nodep/nrfburn/host/hiddev.cpp

/* Name: hiddata.c
 * Author: Christian Starkjohann
 * Creation Date: 2008-04-11
 * Tabsize: 4
 * Copyright: (c) 2008 by OBJECTIVE DEVELOPMENT Software GmbH
 * License: GNU GPL v2 (see License.txt), GNU GPL v3 or proprietary (CommercialLicense.txt)
 */

#include <stdio.h>
#include <stdint.h>
#include <string>

#include "hiddev.h"

#define USBOPEN_SUCCESS         0   	// no error
#define USBOPEN_ERR_ACCESS      1   	// not enough permissions to open device
#define USBOPEN_ERR_IO          2   	// I/O error
#define USBOPEN_ERR_NOTFOUND    3   	// device not found

#ifdef DEBUG
#define DEBUG_PRINT(arg)    printf arg
#else
#define DEBUG_PRINT(arg)
#endif

#define LOG_HID_TRAFFIC

#include "utils.h"

/* ######################################################################## */
#ifdef WIN32 /* ******##################################################### */
/* ######################################################################## */

#include <windows.h>
#include <setupapi.h>

#include "hidsdi_loc.h"
#include <ddk/hidpi.h>

/* ------------------------------------------------------------------------ */

static void convertUniToAscii(char* buffer)
{
	wchar_t* uni = (wchar_t*)buffer;
	char* ascii = buffer;

	while (*uni != 0)
	{
		*ascii++ = *uni > 0xff ? '?' : *uni;
		uni++;
	}

	*ascii++ = '\0';
}

void log_str(const std::string& str)
{
	static FILE* fLog = NULL;
	
	if (fLog == NULL)
		fLog = fopen("nrfburn.txt", "a");
	
	if (fLog)
		fprintf(fLog, str.c_str());
}

std::string GetErrorString(int error)
{
	LPVOID lpMsgBuf;

	FormatMessage(	FORMAT_MESSAGE_ALLOCATE_BUFFER | FORMAT_MESSAGE_FROM_SYSTEM | FORMAT_MESSAGE_IGNORE_INSERTS,
					NULL,
					error,
					MAKELANGID(LANG_NEUTRAL, SUBLANG_DEFAULT), // Default language
					(LPTSTR) &lpMsgBuf,
					0,
					NULL);

	std::string ret_val((char*)lpMsgBuf);

	LocalFree(lpMsgBuf);

	return ret_val;
}

int usbhidOpenDevice(usbDevice_t** device, int vendor, const char* vendorName, int product, const char* productName)
{
	GUID                                hidGuid;        	// GUID for HID driver
	HDEVINFO                            deviceInfoList;
	SP_DEVICE_INTERFACE_DATA            deviceInfo;
	SP_DEVICE_INTERFACE_DETAIL_DATA*    deviceDetails = NULL;
	DWORD                               size;
	int                                 i, openFlag = 0;	// may be FILE_FLAG_OVERLAPPED
	int                                 errorCode = USBOPEN_ERR_NOTFOUND;
	HANDLE                              handle = INVALID_HANDLE_VALUE;
	HIDD_ATTRIBUTES                     deviceAttributes;

	HidD_GetHidGuid(&hidGuid);
	deviceInfoList = SetupDiGetClassDevs(&hidGuid, NULL, NULL, DIGCF_PRESENT | DIGCF_INTERFACEDEVICE);
	deviceInfo.cbSize = sizeof(deviceInfo);
	for (i = 0;; i++)
	{
		if (handle != INVALID_HANDLE_VALUE)
		{
			CloseHandle(handle);
			handle = INVALID_HANDLE_VALUE;
		}

		if (!SetupDiEnumDeviceInterfaces(deviceInfoList, 0, &hidGuid, i, &deviceInfo))
			break;  // no more entries

		// first do a dummy call just to determine the actual size required
		SetupDiGetDeviceInterfaceDetail(deviceInfoList, &deviceInfo, NULL, 0, &size, NULL);
		if (deviceDetails != NULL)
			free(deviceDetails);
		deviceDetails = (SP_DEVICE_INTERFACE_DETAIL_DATA*) malloc(size);
		deviceDetails->cbSize = sizeof(*deviceDetails);

		// this call is for real:
		SetupDiGetDeviceInterfaceDetail(deviceInfoList, &deviceInfo, deviceDetails, size, &size, NULL);
		//log_str("checking HID path " + std::string(deviceDetails->DevicePath) + "\n");

		// attempt opening for R/W -- we don't care about devices which can't be accessed
		handle = CreateFile(deviceDetails->DevicePath, GENERIC_READ | GENERIC_WRITE, FILE_SHARE_READ | FILE_SHARE_WRITE, NULL, OPEN_EXISTING, openFlag, NULL);
		if (handle == INVALID_HANDLE_VALUE)
		{
			//log_str("opening failed: " + GetErrorString(GetLastError()) + "\n");
			// errorCode = USBOPEN_ERR_ACCESS; opening will always fail for mouse -- ignore
			continue;
		}

		deviceAttributes.Size = sizeof(deviceAttributes);
		HidD_GetAttributes(handle, &deviceAttributes);
		//log_str("device attributes: vid=" + int2str(deviceAttributes.VendorID) + " pid=" + int2str(deviceAttributes.ProductID) + "\n");
		if (deviceAttributes.VendorID != vendor || deviceAttributes.ProductID != product)
			continue;   // ignore this device

		errorCode = USBOPEN_ERR_NOTFOUND;
		if (vendorName != NULL  &&  productName != NULL)
		{
			char buffer[512];
			if (!HidD_GetManufacturerString(handle, buffer, sizeof(buffer)))
			{
				log_str("error obtaining vendor name\n");
				errorCode = USBOPEN_ERR_IO;
				continue;
			}

			convertUniToAscii(buffer);

			log_str("vendorName = " + std::string(buffer) + "\n");
			if (strcmp(vendorName, buffer) != 0)
				continue;

			if (!HidD_GetProductString(handle, buffer, sizeof(buffer)))
			{
				log_str("error obtaining product name\n");
				errorCode = USBOPEN_ERR_IO;
				continue;
			}

			convertUniToAscii(buffer);

			log_str("productName = " + std::string(buffer) + "\n");
			if (strcmp(productName, buffer) != 0)
				continue;
		}

		break;  // we have found the device we are looking for!
	}

	SetupDiDestroyDeviceInfoList(deviceInfoList);

	if (deviceDetails != NULL)
		free(deviceDetails);

	if (handle != INVALID_HANDLE_VALUE)
	{
		*device = (usbDevice_t*)handle;
		errorCode = USBOPEN_SUCCESS;
	}

	return errorCode;
}

void usbhidCloseDevice(usbDevice_t* device)
{
	CloseHandle((HANDLE)device);
}

int usbhidSetReport(usbDevice_t* device, char* buffer, int len)
{
	BOOLEAN rval = HidD_SetFeature((HANDLE)device, buffer, len);
	if (rval == FALSE)
		log_str("--- HidD_SetFeature(); GetLastError() == " + GetErrorString(GetLastError()) + "\n");

	return rval == 0 ? USBOPEN_ERR_IO : USBOPEN_SUCCESS;
}

int usbhidGetReport(usbDevice_t* device, int reportNumber, char* buffer, int* len)
{
	buffer[0] = reportNumber;
	BOOLEAN rval = HidD_GetFeature((HANDLE)device, buffer, *len);
	if (rval == FALSE)
		log_str("--- HidD_GetFeature(); GetLastError() == " + GetErrorString(GetLastError()) + "\n");
	
	return rval == 0 ? USBOPEN_ERR_IO : USBOPEN_SUCCESS;
}

/* ######################################################################## */
#else /* defined WIN32 #################################################### */
/* ######################################################################## */

#include <string.h>
#include <usb.h>

#define usbDevice  usb_dev_handle		// use libusb's device structure

#define USBRQ_HID_GET_REPORT    0x01
#define USBRQ_HID_SET_REPORT    0x09

#define USB_HID_REPORT_TYPE_FEATURE 3


static int usbhidGetStringAscii(usb_dev_handle* dev, int index, char* buf, int buflen)
{
	char buffer[256];
	int rval, i;

	if ((rval = usb_get_string_simple(dev, index, buf, buflen)) >= 0)		// use libusb version if it works
		return rval;

	if ((rval = usb_control_msg(dev, USB_ENDPOINT_IN, USB_REQ_GET_DESCRIPTOR, (USB_DT_STRING << 8) + index, 0x0409, buffer, sizeof(buffer), 5000)) < 0)
		return rval;

	if (buffer[1] != USB_DT_STRING)
	{
		*buf = 0;
		return 0;
	}

	if ((unsigned char)buffer[0] < rval)
		rval = (unsigned char) buffer[0];

	rval /= 2;

	// lossy conversion to ISO Latin1:
	for (i = 1; i < rval; i++)
	{
		if (i > buflen)			// destination buffer overflow
			break;

		buf[i - 1] = buffer[2 * i];

		if (buffer[2 * i + 1] != 0)		// outside of ISO Latin1 range
			buf[i - 1] = '?';
	}

	buf[i - 1] = 0;

	return i - 1;
}

int usbhidOpenDevice(usbDevice_t** device, int vendor, const char* vendorName, int product, const char* productName)
{
	struct usb_bus*     bus;
	struct usb_device*  dev;
	usb_dev_handle*     handle = NULL;
	int                 errorCode = USBOPEN_ERR_NOTFOUND;
	static int          didUsbInit = 0;

	if (!didUsbInit)
	{
		usb_init();
		didUsbInit = 1;
	}

	usb_find_busses();
	usb_find_devices();

	for (bus = usb_get_busses(); bus; bus = bus->next)
	{
		for (dev = bus->devices; dev; dev = dev->next)
		{
			if (dev->descriptor.idVendor == vendor && dev->descriptor.idProduct == product)
			{
				char    string[256];
				int     len;
				handle = usb_open(dev); // we need to open the device in order to query strings
				if (!handle)
				{
					errorCode = USBOPEN_ERR_ACCESS;
					DEBUG_PRINT(("Warning: cannot open USB device: %s\n", usb_strerror()));
					continue;
				}

				if (vendorName == NULL && productName == NULL)  // name does not matter
					break;

				// now check whether the names match:
				len = usbhidGetStringAscii(handle, dev->descriptor.iManufacturer, string, sizeof(string));
				if (len < 0)
				{
					errorCode = USBOPEN_ERR_IO;
					DEBUG_PRINT(("Warning: cannot query manufacturer for device: %s\n", usb_strerror()));
				} else {
					errorCode = USBOPEN_ERR_NOTFOUND;
					if (strcmp(string, vendorName) == 0)
					{
						len = usbhidGetStringAscii(handle, dev->descriptor.iProduct, string, sizeof(string));
						if (len < 0)
						{
							errorCode = USBOPEN_ERR_IO;
							DEBUG_PRINT(("Warning: cannot query product for device: %s\n", usb_strerror()));
						} else {
							errorCode = USBOPEN_ERR_NOTFOUND;
							if (strcmp(string, productName) == 0)
								break;
						}
					}
				}
				usb_close(handle);
				handle = NULL;
			}
		}

		if (handle)
			break;
	}

	if (handle != NULL)
	{
		errorCode = USBOPEN_SUCCESS;
		*device = (usbDevice_t*)handle;
	}

	return errorCode;
}

void usbhidCloseDevice(usbDevice_t* device)
{
	if (device != NULL)
		usb_close((usb_dev_handle*)device);
}

int usbhidSetReport(usbDevice_t* device, char* buffer, int len)
{
	int bytesSent, reportId = buffer[0];

	bytesSent = usb_control_msg((usb_dev_handle*)device, USB_TYPE_CLASS | USB_RECIP_DEVICE | USB_ENDPOINT_OUT, USBRQ_HID_SET_REPORT, USB_HID_REPORT_TYPE_FEATURE << 8 | (reportId & 0xff), 0, buffer, len, 5000);
	if (bytesSent != len)
	{
		if (bytesSent < 0)
			DEBUG_PRINT((stderr, "Error sending message: %s\n", usb_strerror()));

		return USBOPEN_ERR_IO;
	}

	return USBOPEN_SUCCESS;
}

int usbhidGetReport(usbDevice_t* device, int reportNumber, char* buffer, int* len)
{
	int bytesReceived, maxLen = *len;

	bytesReceived = usb_control_msg((usb_dev_handle*)device, USB_TYPE_CLASS | USB_RECIP_DEVICE | USB_ENDPOINT_IN, USBRQ_HID_GET_REPORT, USB_HID_REPORT_TYPE_FEATURE << 8 | reportNumber, 0, buffer, maxLen, 5000);
	if (bytesReceived < 0)
	{
		DEBUG_PRINT(("Error sending message: %s\n", usb_strerror()));
		return USBOPEN_ERR_IO;
	}

	*len = bytesReceived;

	return USBOPEN_SUCCESS;
}

/* ######################################################################## */
#endif /* defined WIN32 ################################################### */
/* ######################################################################## */


HIDDevice::HIDDevice()
	: hHIDDev(NULL)
{}

HIDDevice::~HIDDevice()
{
	if (hHIDDev != NULL)
		usbhidCloseDevice(hHIDDev);
}

bool HIDDevice::Open(uint16_t vendor_id, const char* vendor_name, uint16_t device_id, const char* device_name)
{
	return usbhidOpenDevice(&hHIDDev, vendor_id, vendor_name, device_id, device_name) == 0;
}

void HIDDevice::GetReport(uint8_t* buffer, int report_size, uint8_t report_id)
{
	log_str("-- into GetRep\n");
	int buff_size = report_size + 1;
	char rcvBuff[buff_size];
	int res = usbhidGetReport(hHIDDev, report_id, rcvBuff, &buff_size);
	if (res != USBOPEN_SUCCESS)
	{
		log_str("Unable to read data from programmer.\n");
		throw std::string("Unable to read data from programmer");
	}

	memcpy(buffer, rcvBuff + 1, report_size);

	log_str("-- GetRep ");
	for (int c = 0; c < report_size; ++c)
		log_str(int2hex(buffer[c]) + " ");
	log_str("\n");
	
	log_str("-- out of GetRep\n");
}

void HIDDevice::SetReport(const uint8_t* buffer, int bytes, int report_size, uint8_t report_id)
{
	log_str("-- SetRep ");
	for (int c = 0; c < bytes; ++c)
		log_str(int2hex(buffer[c]) + " ");
	log_str("\n");

	// alloc and clear the buffer
	int buff_size = report_size + 1;
	char sendbuff[buff_size];
	memset(sendbuff, 0, buff_size);

	// set the report ID and the data
	sendbuff[0] = report_id;
	memcpy(sendbuff + 1, buffer, bytes);

	int result = usbhidSetReport(hHIDDev, sendbuff, buff_size);
	if (result != USBOPEN_SUCCESS)
	{
		log_str("Unable to send data to programmer.\n");
		throw std::string("Unable to send data to programmer.");
	}
	
	log_str("-- out of SetRep\n");
}
